tuliovfarias/Foot-Swich-Zoom-G3-By_TuLiO/Files/ARDUINO-PLACA.png

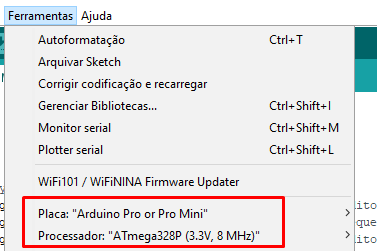
Files/ARDUINO-PLACA.png
