tuliovfarias/Foot-Swich-Zoom-G3-By_TuLiO/Files/Foto.png

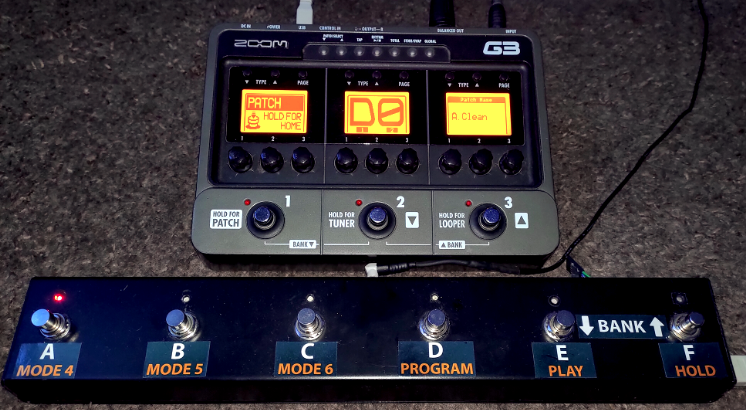
Files/Foto.png
