tuliovfarias/Foot-Swich-Zoom-G3-By_TuLiO/Files/Outros projetos/ZoomControl-master/Esquema.PNG

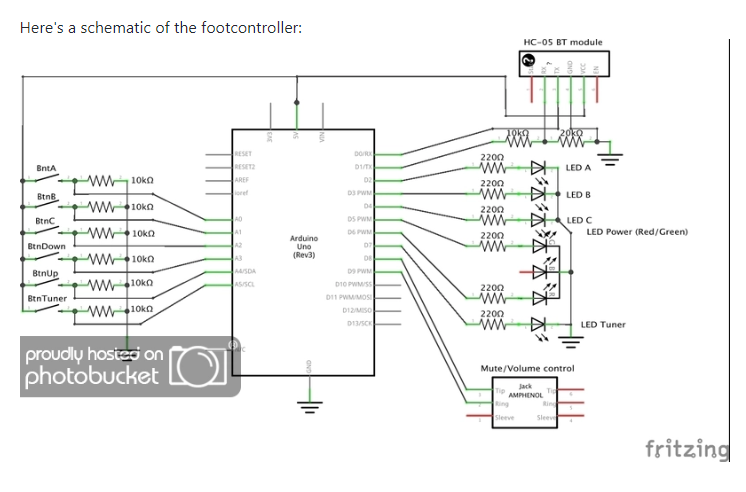
Files/Outros projetos/ZoomControl-master/Esquema.PNG
